LucidVR/lucidgloves/hardware/Prototype5_BETA/GuideRings/GuideRing_v1.2_17mm.STL

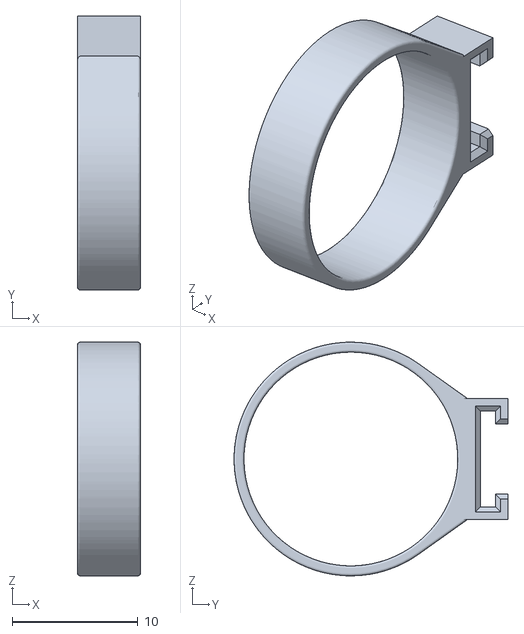
[picture p15: CAD file, 2025-10-25]
hardware/Prototype5_BETA/GuideRings/GuideRing_v1.2_17mm.STL
5.00 x 21.8 x 18.6
