LucidVR/lucidgloves/hardware/Prototype5_BETA/RigidMount_Splay_v4.STL

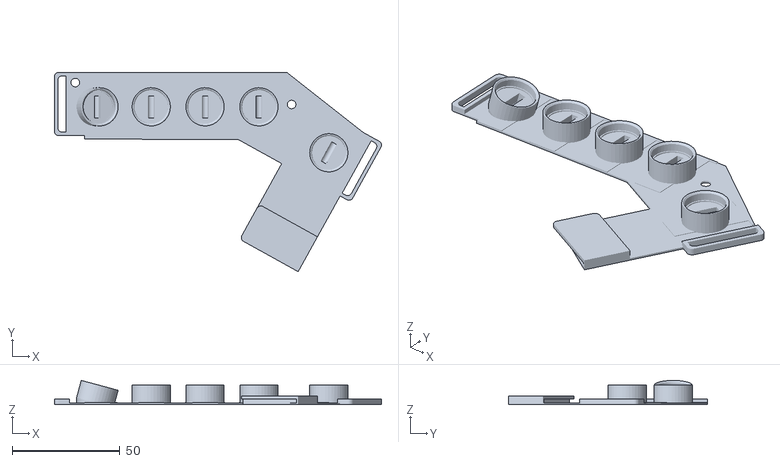
[picture p16: CAD file, 2025-10-25]
hardware/Prototype5_BETA/RigidMount_Splay_v4.STL
151.8 x 92.5 x 11.2
