LucidVR/lucidgloves/hardware/Prototype4.1/WLPotSlideHolder_Proto4.1.STL

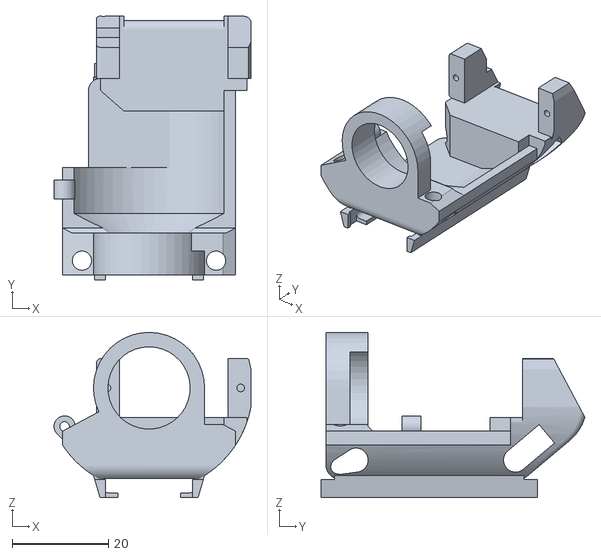
[picture p17: CAD file, 2022-07-16]
hardware/Prototype4.1/WLPotSlideHolder_Proto4.1.STL
41.0 x 54.9 x 34.3
