LucidVR/lucidgloves/hardware/Prototype5_BETA/GuideRings/GuideRing_v1.2_15mm.STL

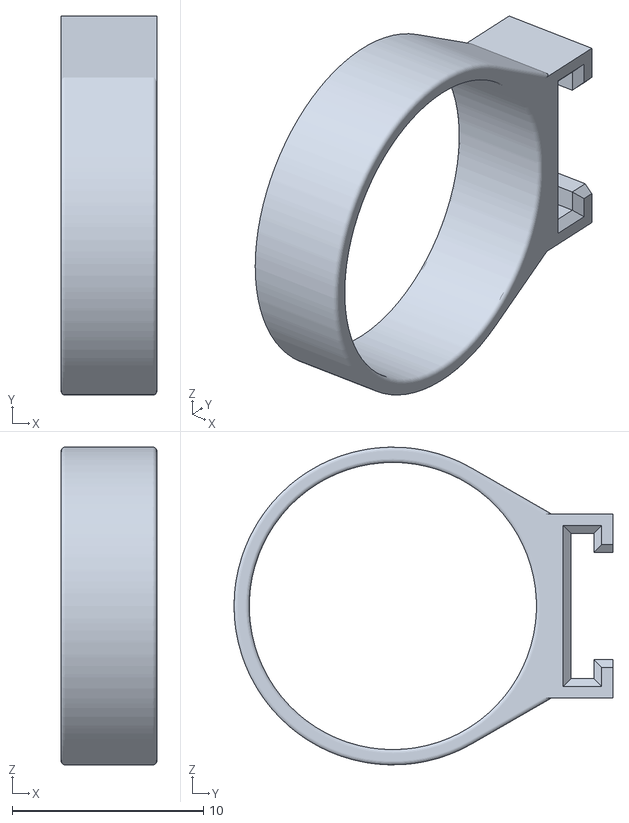
[picture p18: CAD file, 2025-10-25]
hardware/Prototype5_BETA/GuideRings/GuideRing_v1.2_15mm.STL
5.00 x 19.8 x 16.6
