LucidVR/lucidgloves/hardware/Prototype5_BETA/ServoRack_v3.6.STL

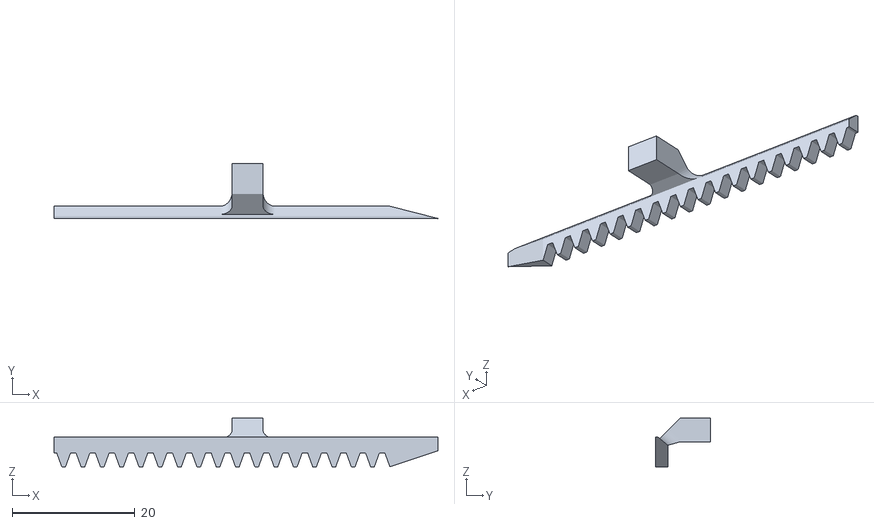
[picture p19: CAD file, 2025-10-25]
hardware/Prototype5_BETA/ServoRack_v3.6.STL
62.5 x 8.95 x 7.90
