LucidVR/lucidgloves/hardware/Prototype4.1/Vive3.0_MountSlider_v1.2.STL

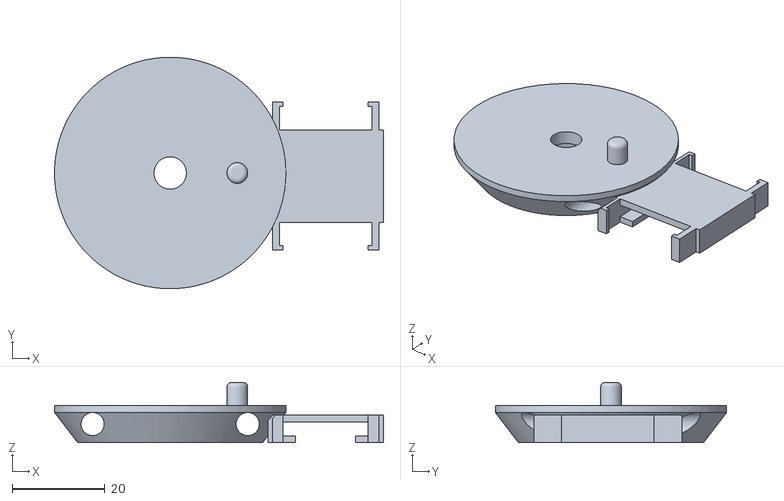
[picture p20: CAD file, 2022-07-16]
hardware/Prototype4.1/Vive3.0_MountSlider_v1.2.STL
71.1 x 50.0 x 13.0
