LucidVR/lucidgloves/hardware/Prototype5_BETA/GuideRings/GuideRing_v1.2_21mm.STL

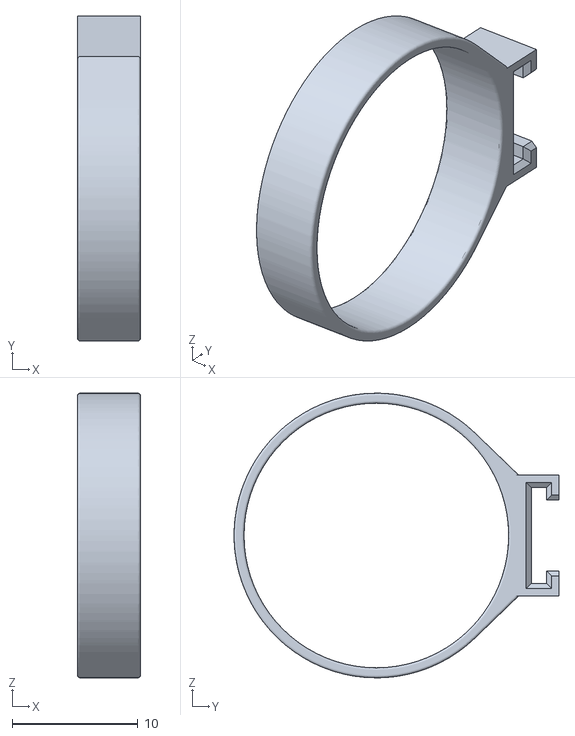
[picture p21: CAD file, 2025-10-25]
hardware/Prototype5_BETA/GuideRings/GuideRing_v1.2_21mm.STL
5.00 x 25.8 x 22.6
