LucidVR/lucidgloves/hardware/Prototype5_BETA/MagnetPinion_v5.3.STL

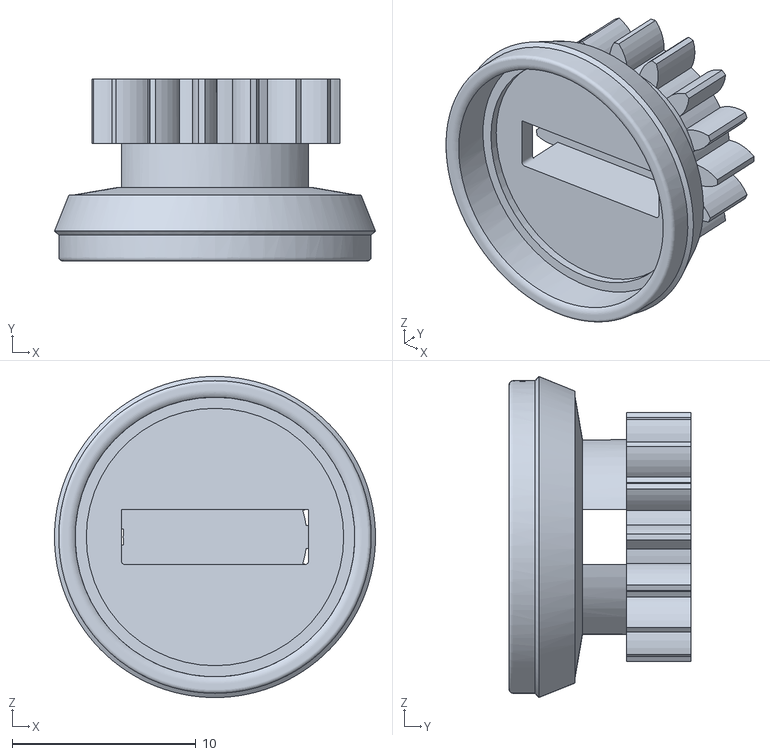
[picture p22: CAD file, 2025-10-25]
hardware/Prototype5_BETA/MagnetPinion_v5.3.STL
17.5 x 9.90 x 17.5
