LucidVR/lucidgloves/hardware/Prototype4.1/WLPotElasticHolder_Proto4.1.STL

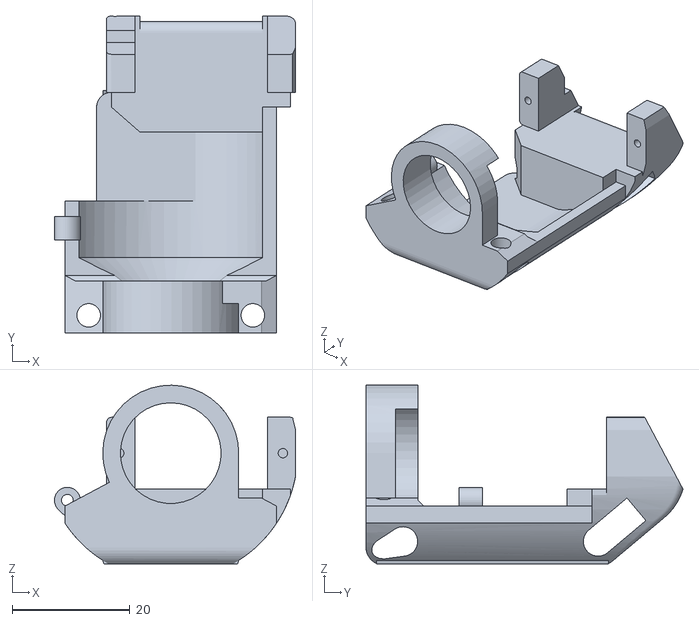
[picture p23: CAD file, 2022-07-16]
hardware/Prototype4.1/WLPotElasticHolder_Proto4.1.STL
41.0 x 53.9 x 30.3
