LucidVR/lucidgloves/hardware/Prototype5_BETA/SensorTop_v4.0.STL

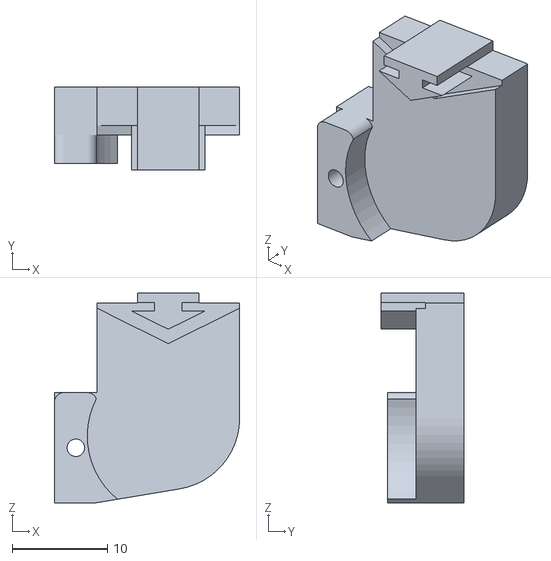
[picture p24: CAD file, 2025-10-25]
hardware/Prototype5_BETA/SensorTop_v4.0.STL
19.5 x 8.72 x 22.1
