LucidVR/lucidgloves/hardware/Prototype5_BETA/BearingRetainer_v1.2.STL

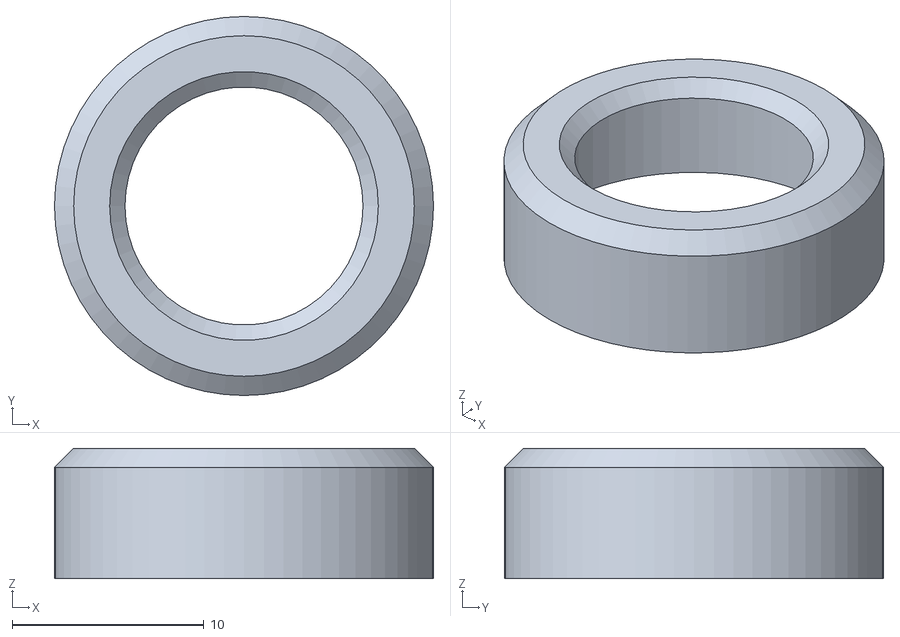
[picture p25: CAD file, 2025-10-25]
hardware/Prototype5_BETA/BearingRetainer_v1.2.STL
19.8 x 19.8 x 6.80
