LucidVR/lucidgloves/hardware/Prototype5_BETA/ServoGear_v3.3.STL

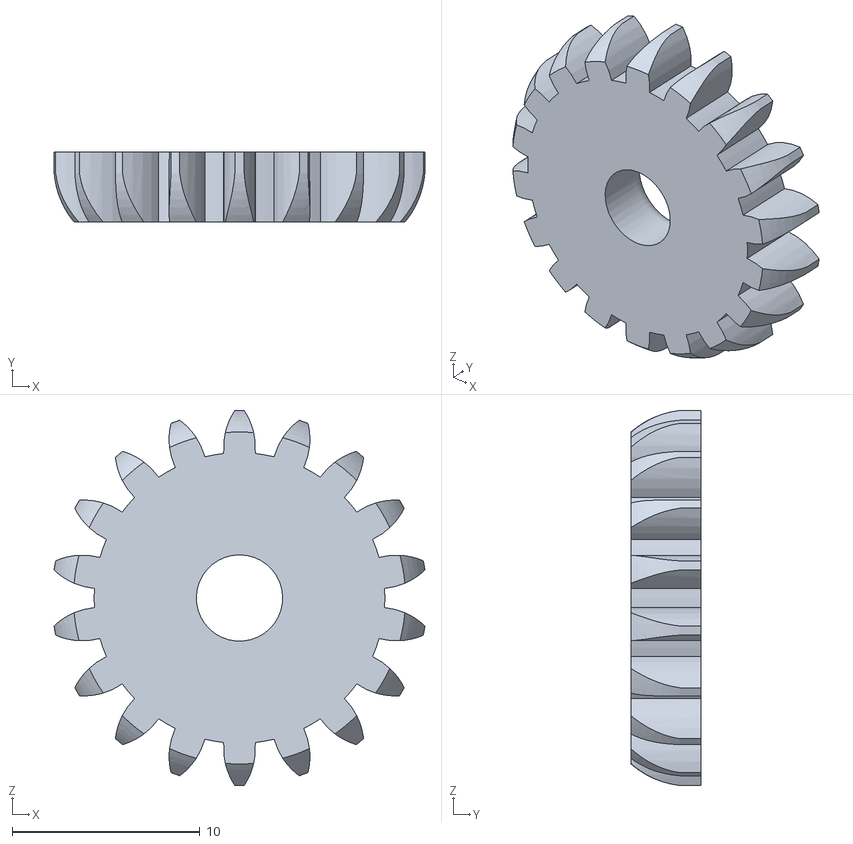
[picture p26: CAD file, 2025-10-25]
hardware/Prototype5_BETA/ServoGear_v3.3.STL
19.8 x 3.75 x 20.0
