LucidVR/lucidgloves/hardware/Prototype5_BETA/FingerRack_v5.2.STL

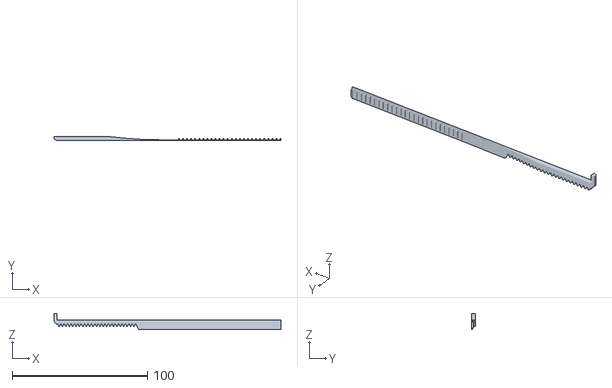
[picture p27: CAD file, 2025-10-25]
hardware/Prototype5_BETA/FingerRack_v5.2.STL
167.8 x 3.00 x 12.0
