LucidVR/lucidgloves/firmware/lucidgloves-firmware/src/Communication/SerialCommunication.h

#pragma once
#include "ICommunication.h"
#include "../../Config.h"
#include <Arduino.h>

class SerialCommunication : public ICommunication {
private:
    bool m_isOpen;

public:
    SerialCommunication();

    bool isOpen() override;

    void start() override;

    void output(char* data) override;

    bool readData(char* input) override;
};
