LucidVR/lucidgloves/firmware/lucidgloves-firmware/src/Controller/Gesture.cpp

#include "Gesture.h"

bool Gesture::grabGesture(int *flexion){
  return (flexion[PINKY_IND] + flexion[RING_IND] + flexion[MIDDLE_IND] + flexion[INDEX_IND]) / 4 <= ANALOG_MAX/2 ? 0:1;
}

bool Gesture::pinchGesture(int *flexion){
  return (flexion[INDEX_IND] + flexion[THUMB_IND]) / 2 <= ANALOG_MAX/2 ? 0:1;
}

bool Gesture::triggerGesture(int *flexion){
  return flexion[INDEX_IND]<=(ANALOG_MAX/2)?0:1;
}
